quintuple-lained/TheWandgame2025/004_IMAGES/TheENDGAME_back.png

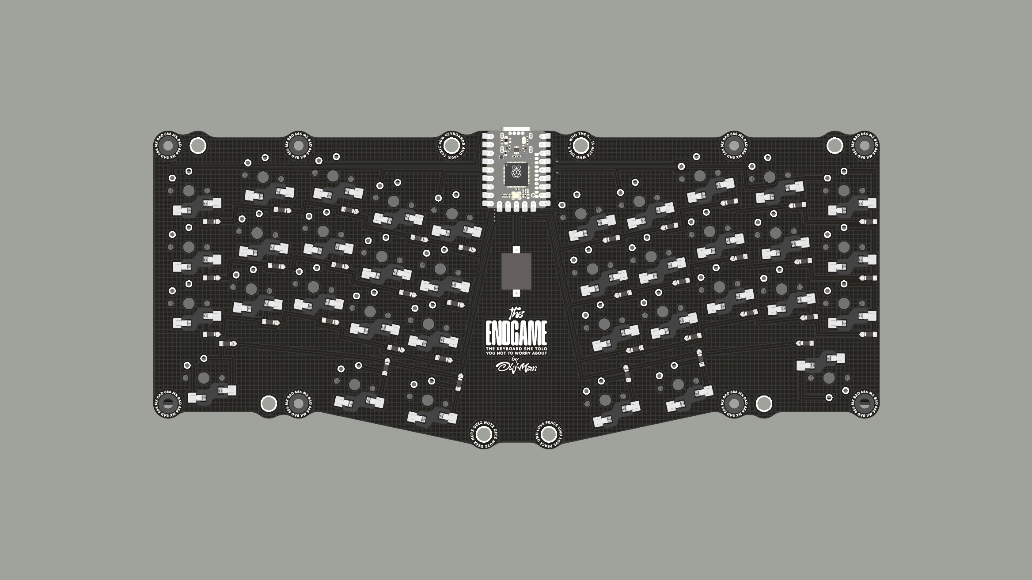
004_IMAGES/TheENDGAME_back.png
