quintuple-lained/TheWandgame2025/004_IMAGES/TheEndgameMood.jpg

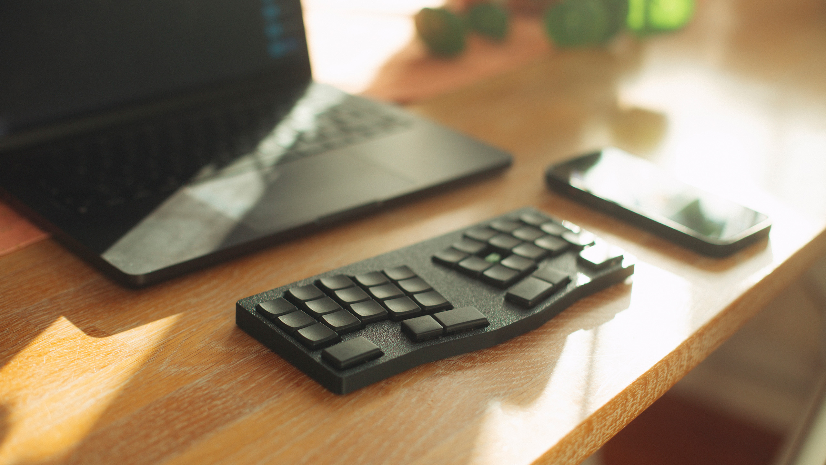
004_IMAGES/TheEndgameMood.jpg
