quintuple-lained/TheWandgame2025/001_PCB/KICAD/COPPER KICAD/TheENDGAME2024_COPPER.kicad_sch

## KiCad design 001_PCB/KICAD/COPPER KICAD/TheENDGAME2024_COPPER.kicad_sch (2025-01-14)

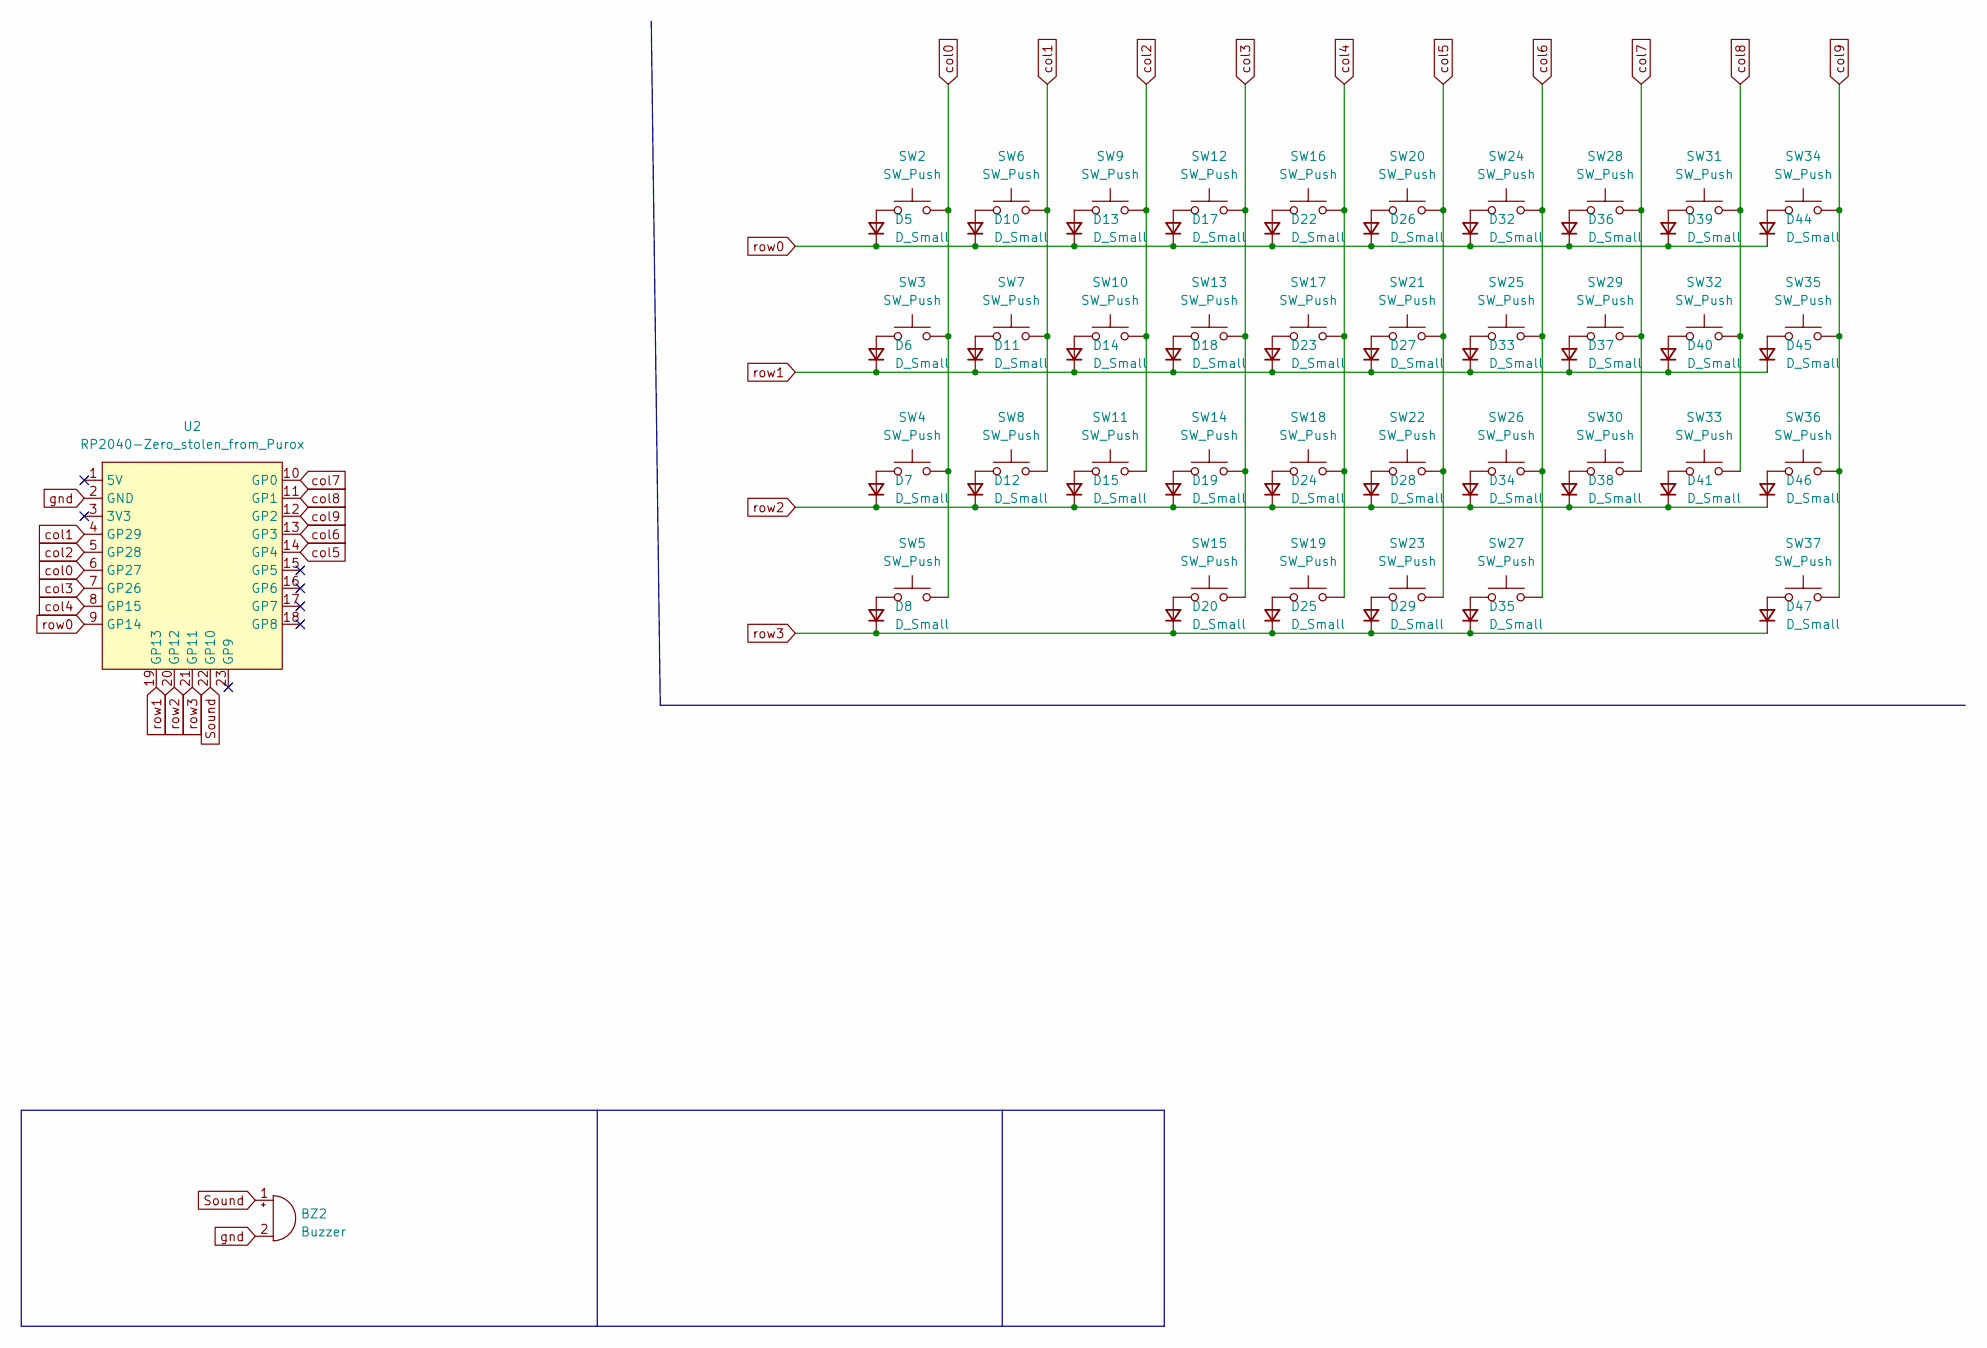
[picture p9: schematic TheENDGAME2024_COPPER.kicad_sch]

Parts:
BZ2: Buzzer; Buzzer_Mallory_AST1109MLTRQ
D5, D6, D7, D8, D10, D11, D12, D13, D14, D15, D17, D18, D19, D20, D22, D23, D24, D25, D26, D27, D28, D29, D32, D33, D34, D35, D36, D37, D38, D39, D40, D41, D44, D45, D46, D47: D_Small; Diode_SOD123 filets triangle
SW2, SW3, SW4, SW6, SW7, SW8, SW9, SW10, SW11, SW12, SW13, SW14, SW15, SW16, SW17, SW18, SW20, SW21, SW22, SW24, SW25, SW26, SW27, SW28, SW29, SW30, SW31, SW32, SW33, SW34, SW35, SW36: SW_Push; SW_choc_v1_HSxSolder_1u_filets_MBK_blk fixxed flipped solde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
SW5, SW19, SW23, SW37: SW_Push; SW_choc_v1_HSxSolder_1.5u_filets_MBK_blk fixxed flipped sol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
U2: RP2040-Zero_stolen_from_Purox; RP2040 Zero stolen from Purox bottom facing up 3d model v3

Connections:
unnamed: D5.2 (A), SW2.1
unnamed: D6.2 (A), SW3.1
unnamed: D7.2 (A), SW4.1
unnamed: D8.2 (A), SW5.1
unnamed: D10.2 (A), SW6.1
unnamed: D11.2 (A), SW7.1
unnamed: D12.2 (A), SW8.1
unnamed: D13.2 (A), SW9.1
unnamed: D14.2 (A), SW10.1
unnamed: D15.2 (A), SW11.1
unnamed: D17.2 (A), SW12.1
unnamed: D18.2 (A), SW13.1
unnamed: D19.2 (A), SW14.1
unnamed: D20.2 (A), SW15.1
unnamed: D22.2 (A), SW16.1
unnamed: D23.2 (A), SW17.1
unnamed: D24.2 (A), SW18.1
unnamed: D25.2 (A), SW19.1
unnamed: D26.2 (A), SW20.1
unnamed: D27.2 (A), SW21.1
unnamed: D28.2 (A), SW22.1
unnamed: D29.2 (A), SW23.1
unnamed: D32.2 (A), SW24.1
unnamed: D33.2 (A), SW25.1
unnamed: D34.2 (A), SW26.1
unnamed: D35.2 (A), SW27.1
unnamed: D36.2 (A), SW28.1
unnamed: D37.2 (A), SW29.1
unnamed: D38.2 (A), SW30.1
unnamed: D39.2 (A), SW31.1
unnamed: D40.2 (A), SW32.1
unnamed: D41.2 (A), SW33.1
unnamed: D44.2 (A), SW34.1
unnamed: D45.2 (A), SW35.1
unnamed: D46.2 (A), SW36.1
unnamed: D47.2 (A), SW37.1
Sound: BZ2.1 (-), U2.22 (GP10)
col0: SW2.2, SW3.2, SW4.2, SW5.2, U2.6 (GP27)
col1: SW6.2, SW7.2, SW8.2, U2.4 (GP29)
col2: SW9.2, SW10.2, SW11.2, U2.5 (GP28)
col3: SW12.2, SW13.2, SW14.2, SW15.2, U2.7 (GP26)
col4: SW16.2, SW17.2, SW18.2, SW19.2, U2.8 (GP15)
col5: SW20.2, SW21.2, SW22.2, SW23.2, U2.14 (GP4)
col6: SW24.2, SW25.2, SW26.2, SW27.2, U2.13 (GP3)
col7: SW28.2, SW29.2, SW30.2, U2.10 (GP0)
col8: SW31.2, SW32.2, SW33.2, U2.11 (GP1)
col9: SW34.2, SW35.2, SW36.2, SW37.2, U2.12 (GP2)
gnd: BZ2.2 (+), U2.2 (GND)
row0: D5.1 (K), D10.1 (K), D13.1 (K), D17.1 (K), D22.1 (K), D26.1 (K), D32.1 (K), D36.1 (K), D39.1 (K), D44.1 (K), U2.9 (GP14)
row1: D6.1 (K), D11.1 (K), D14.1 (K), D18.1 (K), D23.1 (K), D27.1 (K), D33.1 (K), D37.1 (K), D40.1 (K), D45.1 (K), U2.19 (GP13)
row2: D7.1 (K), D12.1 (K), D15.1 (K), D19.1 (K), D24.1 (K), D28.1 (K), D34.1 (K), D38.1 (K), D41.1 (K), D46.1 (K), U2.20 (GP12)
row3: D8.1 (K), D20.1 (K), D25.1 (K), D29.1 (K), D35.1 (K), D47.1 (K), U2.21 (GP11)
